nguyen1013/IoT-Modbus-STM32-project/LTspice/Power-consumption-measurement.asc

C1: cap; 100n
C2: cap; 10µ
C3: cap; 100n
D1: diode; 1N4148
D2: diode; 1N4148
D3: diode; 1N5817
D4: diode; 1N5817
I1: current; SINE(0 2.8 50)
R1: res; 10k
R2: res; 2.7k
R3: res; 10k
R4: res; 2.7k
R5: res; 100
R6: res; 2k
R7: res; 2k
R8: res; 200k
R9: res; 200k
R10: res; 1000k
R_load1: res; 10k
R_shunt: res; 0.01
U1: opamp2; LMC6482A/NS
U4: opamp2; LM741/NS
U5: opamp2; LM741/NS
V1: voltage; 12
V3: voltage; 12
Named nets: VCC, VEE, 0, A, B, Vout, 1, 2
.include nat_semi.lib
.tran 0 200m 0 5m
Replace diode 1N5817 by 1N5822 in Kicad
Go to pin PA1
