nguyen1013/IoT-Modbus-STM32-project/LTspice/AC-DC converter.asc

C1: cap; 100µ
D1: diode; 1N4148
D5: diode; 1N4148
D6: diode; 1N4148
D7: diode; 1N4148
D8: diode; 1N4148
R1: res; 120k
R2: res; 10k
R3: res; 10k
R4: res; 10k
R5: res; 10k
R6: res; 2.7k
U1: opamp2; LM741/NS
U2: opamp2; LM741/NS
V1: voltage; 12
V2: voltage; SINE(0 34 50)
V3: voltage; 12
Named nets: A, B, 0, C, VCC, VEE, Vout
.include nat_semi.lib
.tran 0 150m 0 5m
For AC Vrms = 24V, Vmax ~ 34V
Go to pin PA0
