nguyen1013/IoT-Modbus-STM32-project/STM32/11-modbus-slave-node-1/src/sensors/adc_nsl19m51.h

#ifndef ADC_NSL19M51_H_
#define ADC_NSL19M51_H_

#include "../adc.h"
#include "stm32l1xx.h"
#include <stdlib.h>
#include <math.h>
#include "usart2.h"

int32_t read_NLS19M51_lux(void);

#endif /* ADC_NSL19M51_H_ */
