nguyen1013/IoT-Modbus-STM32-project/STM32/12-modbus-slave-node-2/src/usart2.c

#include <usart2.h>

void USART2_Init(void)
{

	RCC->APB1ENR|=0x00020000; 	//set bit 17 (USART2 EN)
	RCC->AHBENR|=0x00000001; 	//enable GPIOA port clock bit 0 (GPIOA EN)
	GPIOA->AFR[0]=0x00000700;	//GPIOx_AFRL p.188,AF7 p.177
	GPIOA->AFR[0]|=0x00007000;	//GPIOx_AFRL p.188,AF7 p.177
	GPIOA->MODER|=0x00000020; 	//MODER2=PA2(TX) to mode 10=alternate function mode. p184
	GPIOA->MODER|=0x00000080; 	//MODER2=PA3(RX) to mode 10=alternate function mode. p184

	USART2->BRR = 0x00000D05; // **9600 baud @ 32 MHz**
	USART2->CR1 = 0x00000008;	//TE bit. p739-740. Enable transmit
	USART2->CR1 |= 0x00000004;	//RE bit. p739-740. Enable receiver
	USART2->CR1 |= 0x00002000;	//UE bit. p739-740. Uart enable
}

void USART2_write(char data)
{
	//wait while TX buffer is empty
	while(!(USART2->SR&0x0080)){} 	//TXE: Transmit data register empty. p736-737
		USART2->DR=(data);		//p739
}

char USART2_read()
{
	char data=0;
	//wait while RX buffer data is ready to be read
	while(!(USART2->SR&0x0020)){} //Bit 5 RXNE: Read data register not empty
		data=USART2->DR;			//p739
		return data;
}

void USART2_WriteString(const char *s)
{
    while (*s)
    {
    	USART2_write(*s++);
    }
}

void USART2_WriteCharArray(const char *str, int32_t maxchars)
{
    int32_t i = 0;
    while (str[i] != '\0' && i < maxchars)
    {
        USART2_write(str[i++]);
    }
    USART2_write('\r');
    USART2_write('\n');
}
