nguyen1013/IoT-Modbus-STM32-project/STM32/11-modbus-slave-node-1/src/timer.h

/*
 * timer.h
 *
 *  Created on: 27 thg 11, 2025
 *      Author: nguyen
 */

#ifndef TIMER_H_
#define TIMER_H_

void timer3_Init(void);
void timer11_init(void);
void delay_ms(unsigned long delay);
void delay_10us(void);


#endif /* TIMER_H_ */
